wyu4/droneanator-9000/src/Telemetry/Logger.h

#include <Arduino.h>


/**
 * @brief Initializes everything needed to log data.
 *
 */
void setupLogger();

/**
 * @brief Print a message to the logger
 *
 * @param message Message to log
 */
void println(const char message[]);

/**
 * @brief Print a message to the logger
 *
 * @param message Message to log
 */
void println(const String message);

/**
 * @brief Print a formatted string to the logger
 * 
 * @param format Formatted string
 * @param ... Parameters
 */
void printformat(const char *format, ...);


/**
 * @brief Sends IMU data
 * 
 * @param imu Euler and quaternion values read from the IMU (1: euler_x, 2: euler_y, 3: euler_z, 4: quat_x, 5: quat_y, 6: quat_z, 7: quat_w)
 */
void sendIMU(float imu[7]);

/**
 * @brief Enable/Disable the drone's ability to connect with a laptop
 * 
 * @param enabled True if enabled, else False
 */
void setPairingMode(const bool enabled);

void writeUDPF(const char *format, ...);
